plocher/PCR-Badge-2015/IMG_0888.jpg

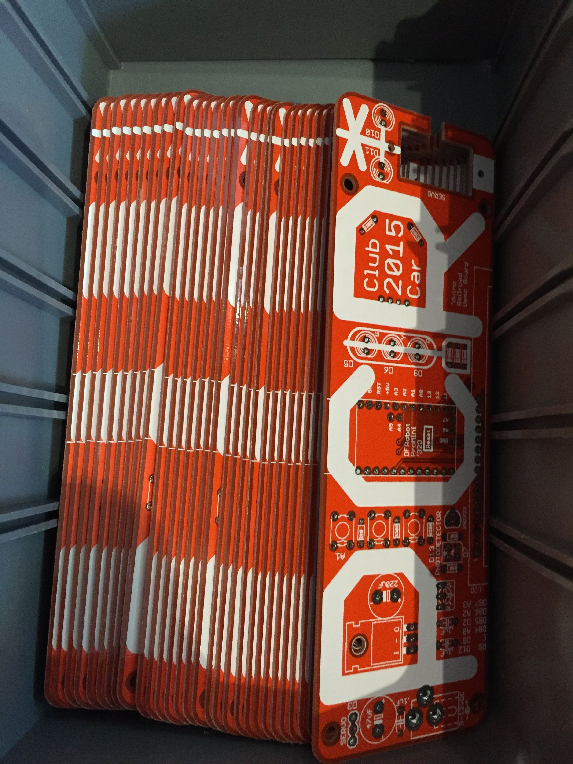
IMG_0888.jpg
